Ha22yX/Mother-Ship-Docking-Drone-System/hardware/solidworks/电磁铁连接件.SLDPRT

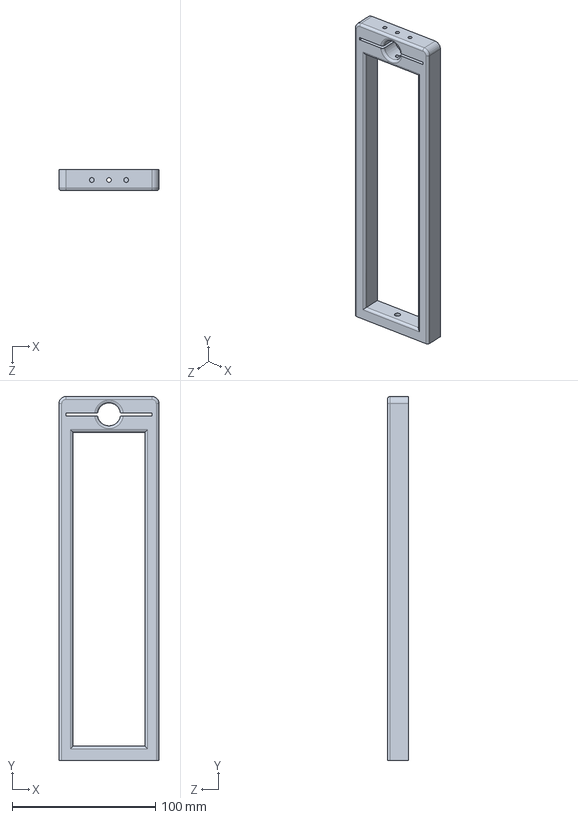
[picture p19: CAD file, 2026-07-10]
hardware/solidworks/电磁铁连接件.SLDPRT
70.0 x 254.0 x 15.0 mm
