Ha22yX/Mother-Ship-Docking-Drone-System/hardware/solidworks/电池仓V2.SLDPRT

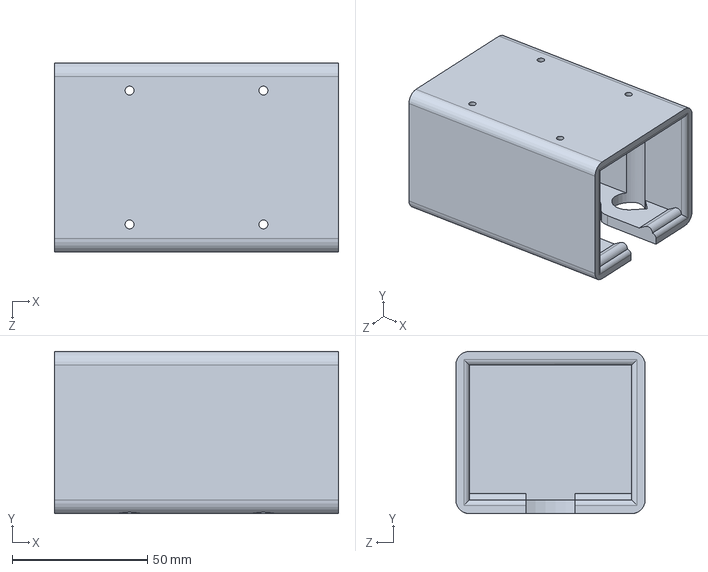
[picture p20: CAD file, 2026-07-10]
hardware/solidworks/电池仓V2.SLDPRT
105.0 x 60.0 x 70.0 mm
