Ha22yX/Mother-Ship-Docking-Drone-System/hardware/solidworks/贴片连接件简化版.SLDPRT

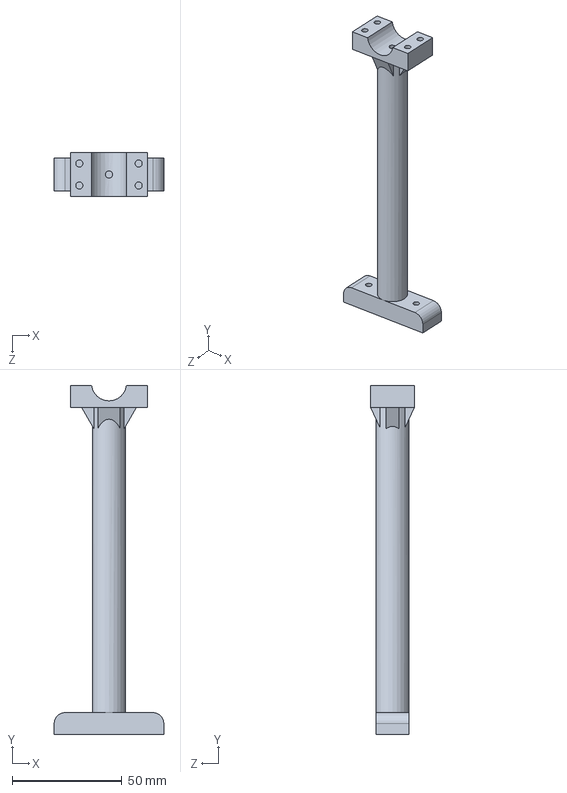
[picture p21: CAD file, 2026-07-10]
hardware/solidworks/贴片连接件简化版.SLDPRT
50.0 x 159.0 x 20.0 mm
