Ha22yX/Mother-Ship-Docking-Drone-System/hardware/solidworks/电机.SLDPRT

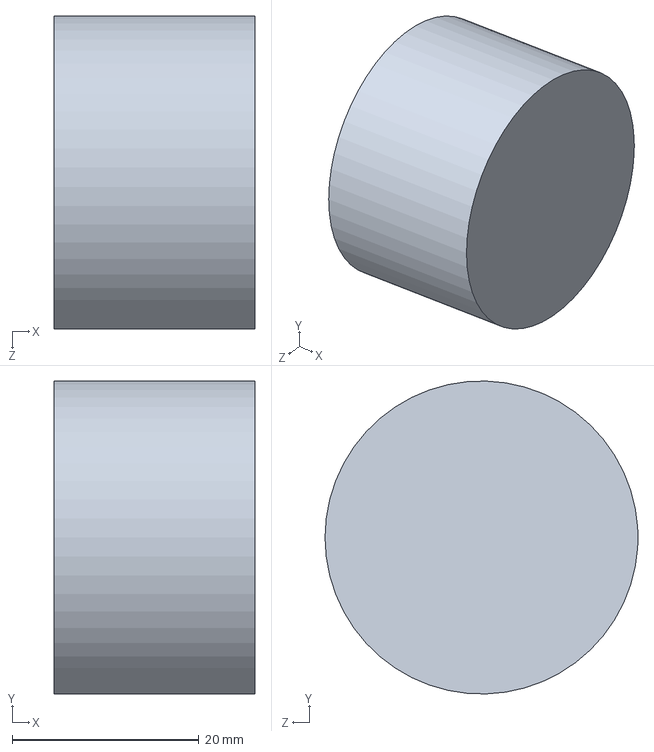
[picture p22: CAD file, 2026-07-10]
hardware/solidworks/电机.SLDPRT
21.5 x 33.5 x 33.5 mm
