Ha22yX/Mother-Ship-Docking-Drone-System/hardware/solidworks/圆管夹片.SLDPRT

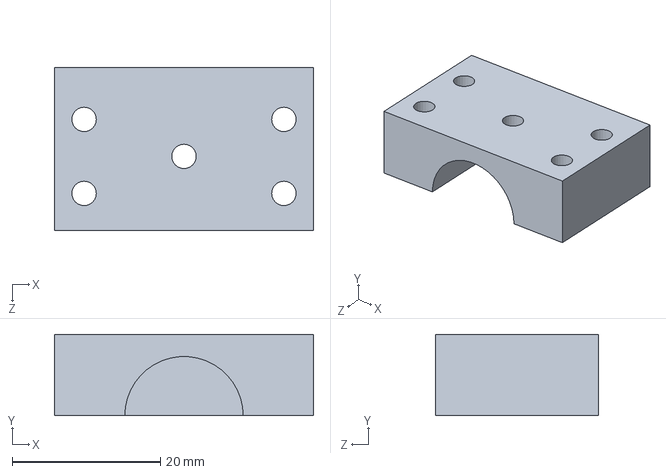
[picture p23: CAD file, 2026-07-10]
hardware/solidworks/圆管夹片.SLDPRT
35.0 x 11.0 x 22.0 mm
