Ha22yX/Mother-Ship-Docking-Drone-System/hardware/solidworks/GPS支架V2.SLDPRT

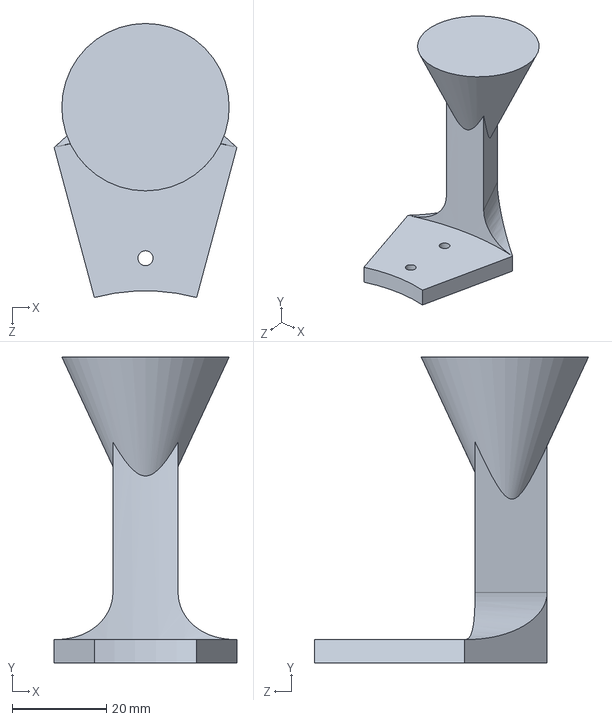
[picture p24: CAD file, 2026-07-10]
hardware/solidworks/GPS支架V2.SLDPRT
38.8 x 65.0 x 58.2 mm
