Ha22yX/Mother-Ship-Docking-Drone-System/gps_drift_test/sessions/20260218_080640/gps_drift_xy.png

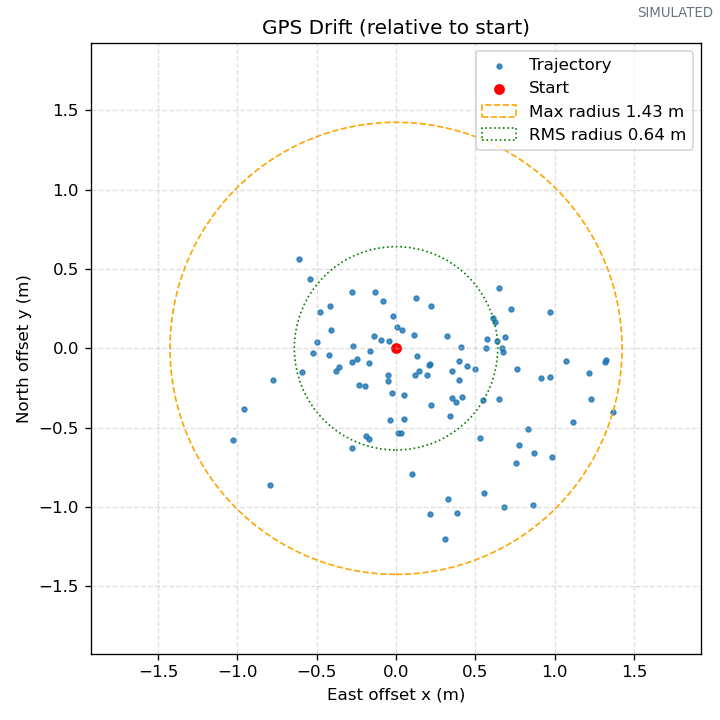
gps_drift_test/sessions/20260218_080640/gps_drift_xy.png
