Ha22yX/Mother-Ship-Docking-Drone-System/gps_drift_test/sessions/20260218_081100/gps_satellites_over_time.png

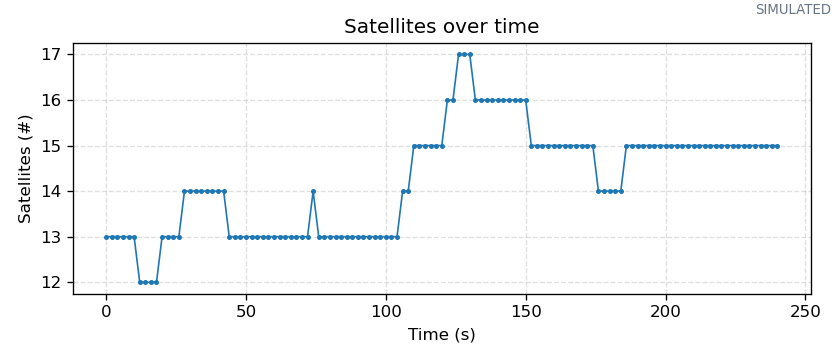
gps_drift_test/sessions/20260218_081100/gps_satellites_over_time.png
